bcancinov/mdc-power-n6-umodule/sim/LTM4651.asc

&1: fraprobe
@1: fra; delay=1.5m fstart=937.5 fend=240K oct=2 fcoarse=7.5K pp0=192m pp1=12m f0=937.5 f1=15K tavgmin=50µ tsettle=66.6667µ
C1: cap; 22µ; Rser=40m Lser=1.7n
C2: cap; 4.7µ
C3: cap; 33n
C4: cap; 10p
C5: cap; 1µ
C6: cap; 100µ; Rser=80m Lser=3n
C7: cap; 12.608µ; Rser=2.172m Lser=0.2n
Coc1: cap; 39.1µ; x4; Rser=2.17m Lser=0.2n
I2: current; PWL(0 0.01 1m 0.01 1.00001m 0.5)
R1: res; 120k
R2: res; 62.5k
R3: res; '6/3'
R4: res; 4.75k
R5: res; 24.9
R6: res; 0.5
R7: res; '6/3'
R8: res; 0.3
U1: LTM4651
U2: XGL4020
V1: voltage; 12
V2: voltage; PULSE(0 3.3 0 1e-9 1e-9 0.25e-6 0.5e-6)
Named nets: 0, IN, OUT, ldo
.tran 2.2m startup
.fra startup
